gustavohbf/robotoy/design/explosion/explosion0031.png

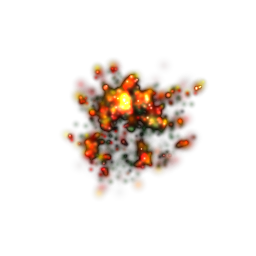
design/explosion/explosion0031.png
