gustavohbf/robotoy/design/3dprint/turret/turret_sliced.PNG

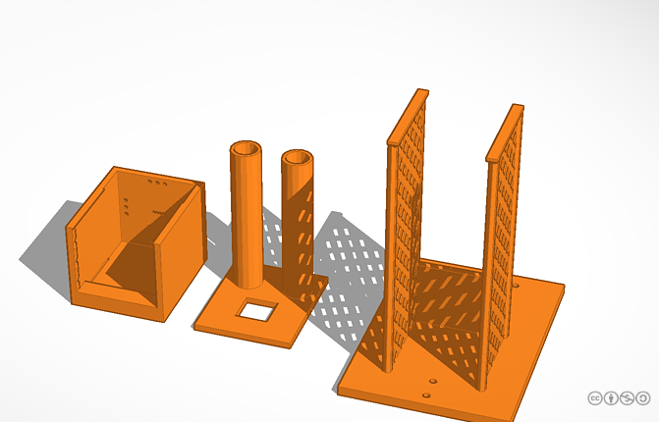
design/3dprint/turret/turret_sliced.PNG
