gustavohbf/robotoy/design/explosion/explosion0000.png

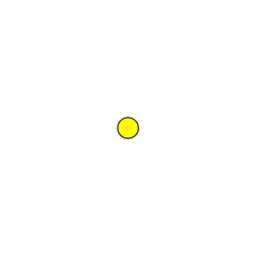
design/explosion/explosion0000.png
