gustavohbf/robotoy/design/explosion/explosion0010.png

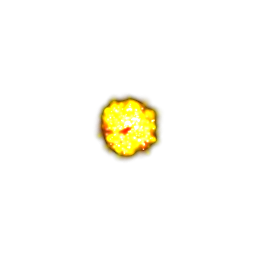
design/explosion/explosion0010.png
