gustavohbf/robotoy/design/explosion/explosion0013.png

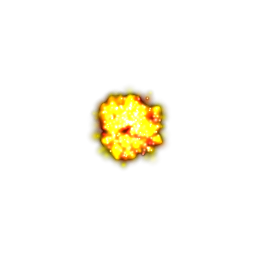
design/explosion/explosion0013.png
