gustavohbf/robotoy/design/explosion/explosion0029.png

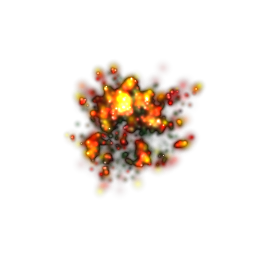
design/explosion/explosion0029.png
