gustavohbf/robotoy/design/explosion/explosion0035.png

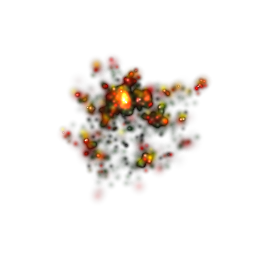
design/explosion/explosion0035.png
