gustavohbf/robotoy/design/explosion/explosion0038.png

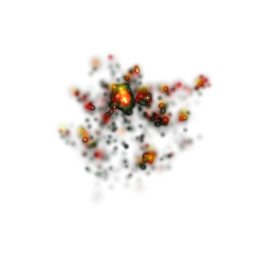
design/explosion/explosion0038.png
