gustavohbf/robotoy/design/explosion/explosion0042.png

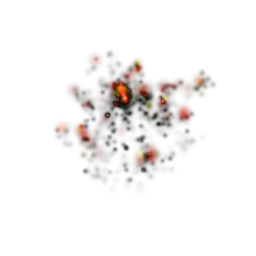
design/explosion/explosion0042.png
