gustavohbf/robotoy/design/explosion/explosion0047.png

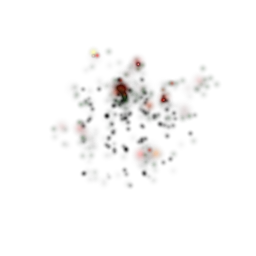
design/explosion/explosion0047.png
