gustavohbf/robotoy/design/explosion/explosion0051.png

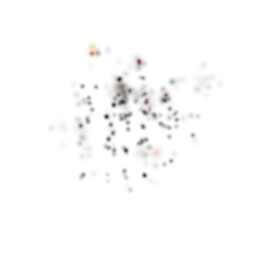
design/explosion/explosion0051.png
