gustavohbf/robotoy/design/explosion/explosion0057.png

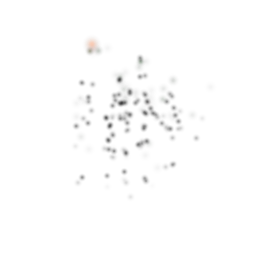
design/explosion/explosion0057.png
