gustavohbf/robotoy/design/explosion/explosion0066.png

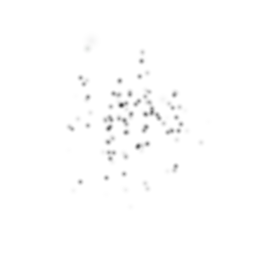
design/explosion/explosion0066.png
