gustavohbf/robotoy/design/explosion/explosion0075.png

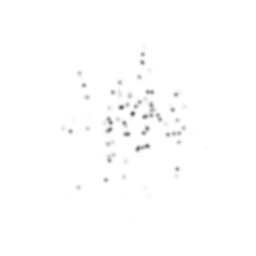
design/explosion/explosion0075.png
