gustavohbf/robotoy/design/explosion/explosion0084.png

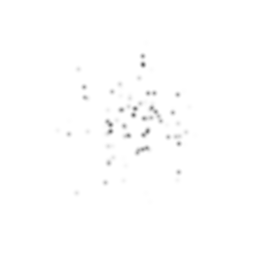
design/explosion/explosion0084.png
