gustavohbf/robotoy/design/explosion/explosion0100.png

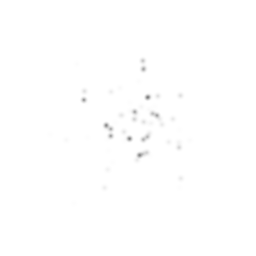
design/explosion/explosion0100.png
