gustavohbf/robotoy/design/explosion/explosion0104.png

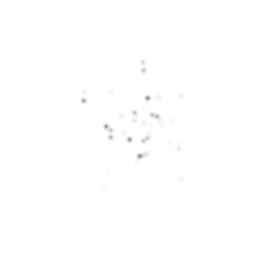
design/explosion/explosion0104.png
