gustavohbf/robotoy/design/explosion/explosion0119.png

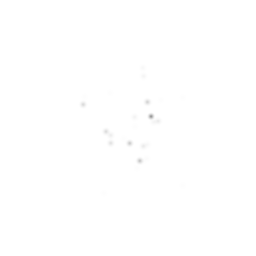
design/explosion/explosion0119.png
