gustavohbf/robotoy/design/sketch/RoboToy_bb.png

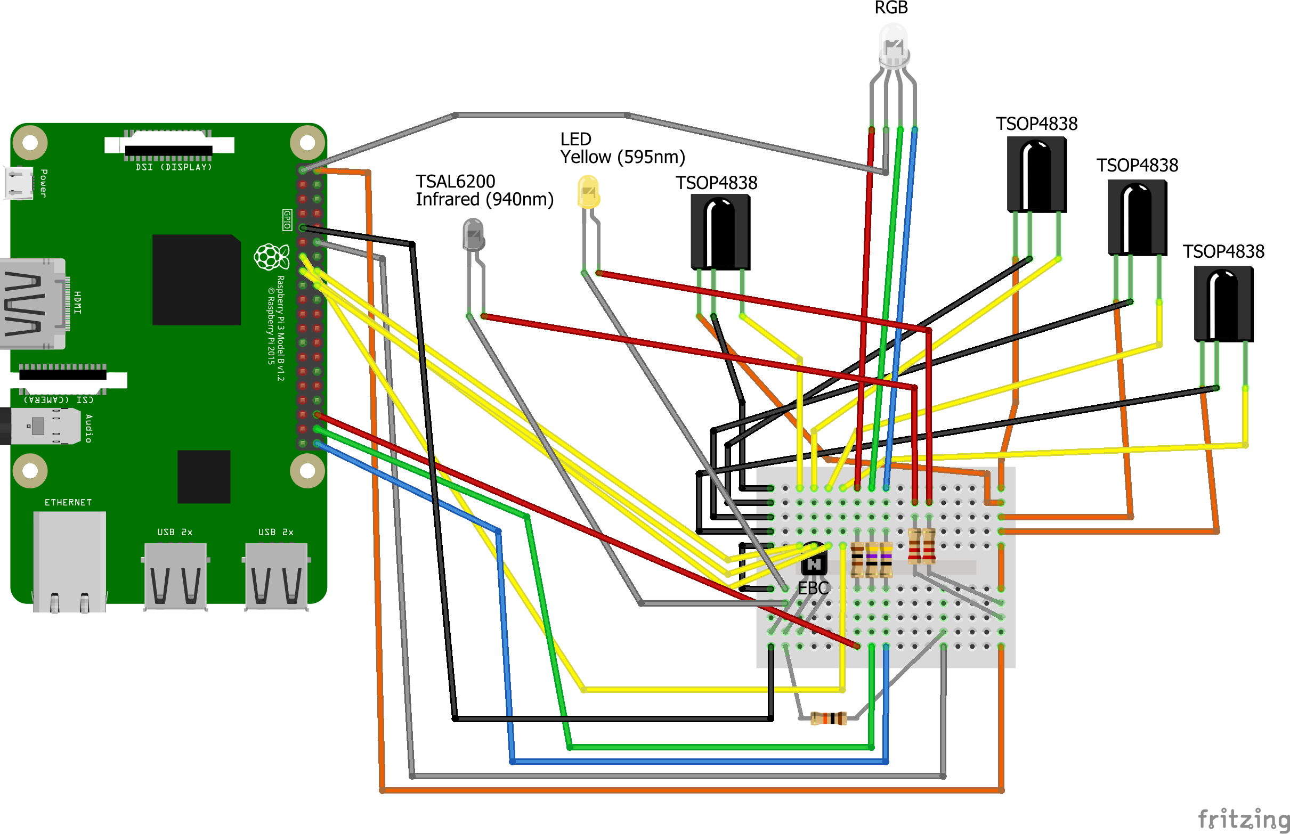
design/sketch/RoboToy_bb.png
