gustavohbf/robotoy/design/sketch/RoboToy_Schematic.png

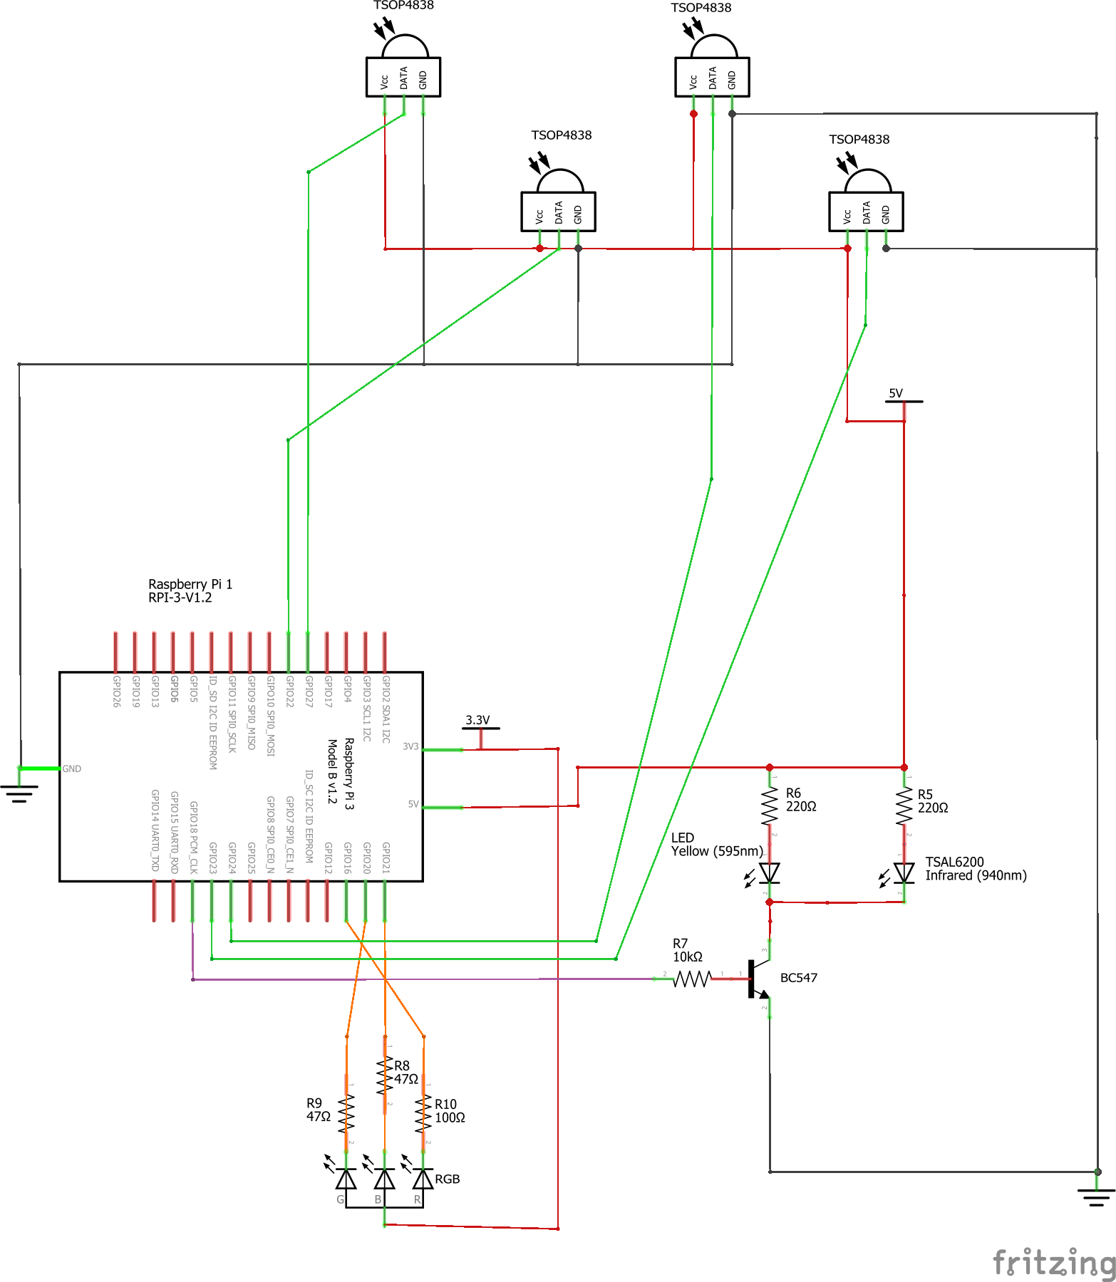
design/sketch/RoboToy_Schematic.png
