gustavohbf/robotoy/src/main/java/org/guga/robotoy/rasp/res/images/background.jpg

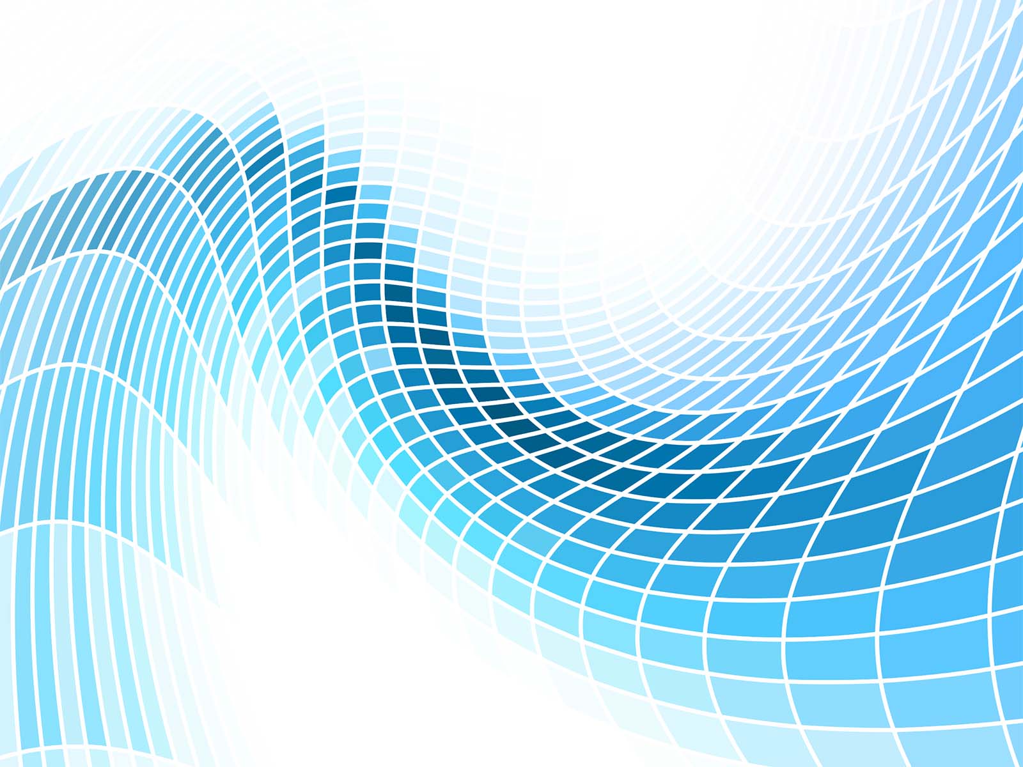
src/main/java/org/guga/robotoy/rasp/res/images/background.jpg
