gustavohbf/robotoy/src/main/java/org/guga/robotoy/rasp/res/images/bigexplosion.png

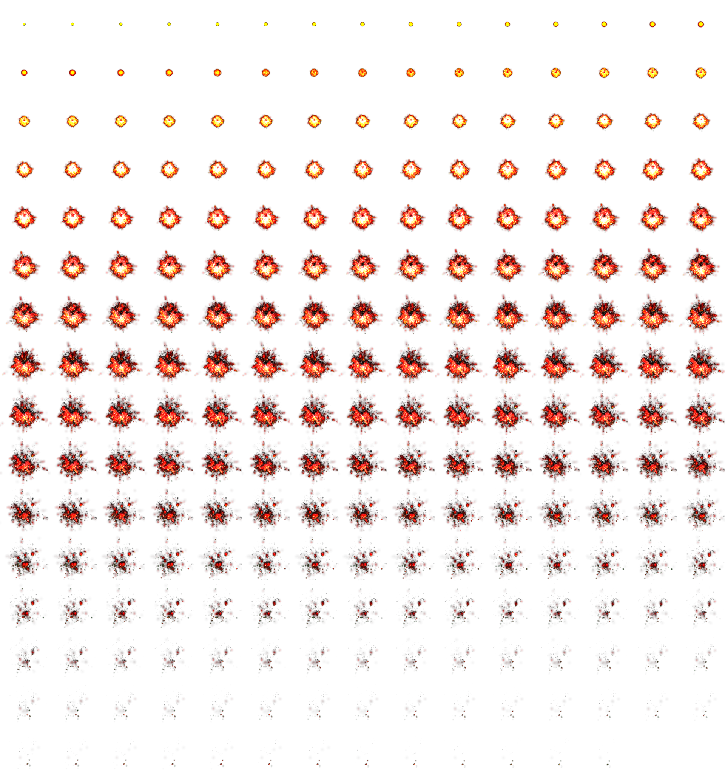
src/main/java/org/guga/robotoy/rasp/res/images/bigexplosion.png
