gustavohbf/robotoy/src/main/java/org/guga/robotoy/rasp/res/images/down.png

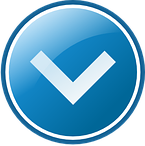
src/main/java/org/guga/robotoy/rasp/res/images/down.png
