gustavohbf/robotoy/src/main/java/org/guga/robotoy/rasp/res/images/engine.png

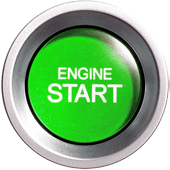
src/main/java/org/guga/robotoy/rasp/res/images/engine.png
