gustavohbf/robotoy/src/main/java/org/guga/robotoy/rasp/res/images/explosion.png

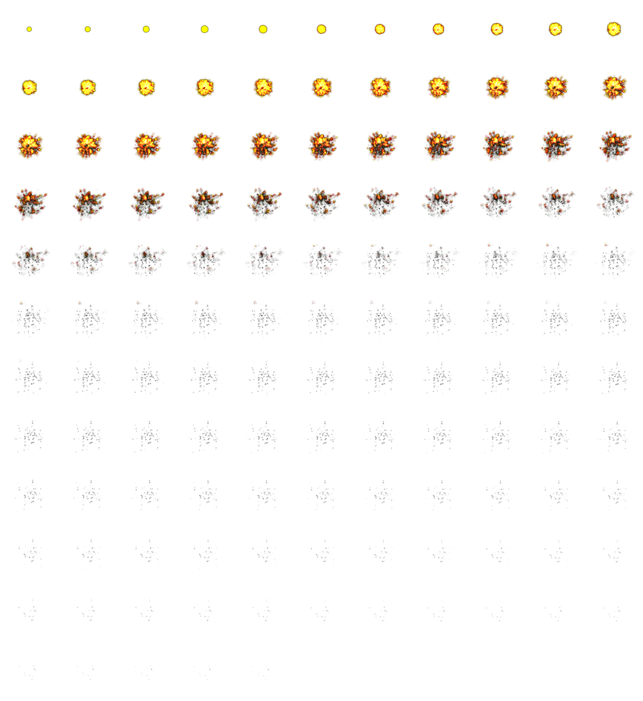
src/main/java/org/guga/robotoy/rasp/res/images/explosion.png
