gustavohbf/robotoy/src/main/java/org/guga/robotoy/rasp/res/images/fire.png

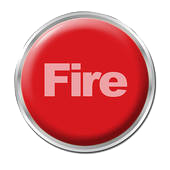
src/main/java/org/guga/robotoy/rasp/res/images/fire.png
