gustavohbf/robotoy/src/main/java/org/guga/robotoy/rasp/res/images/heart.png

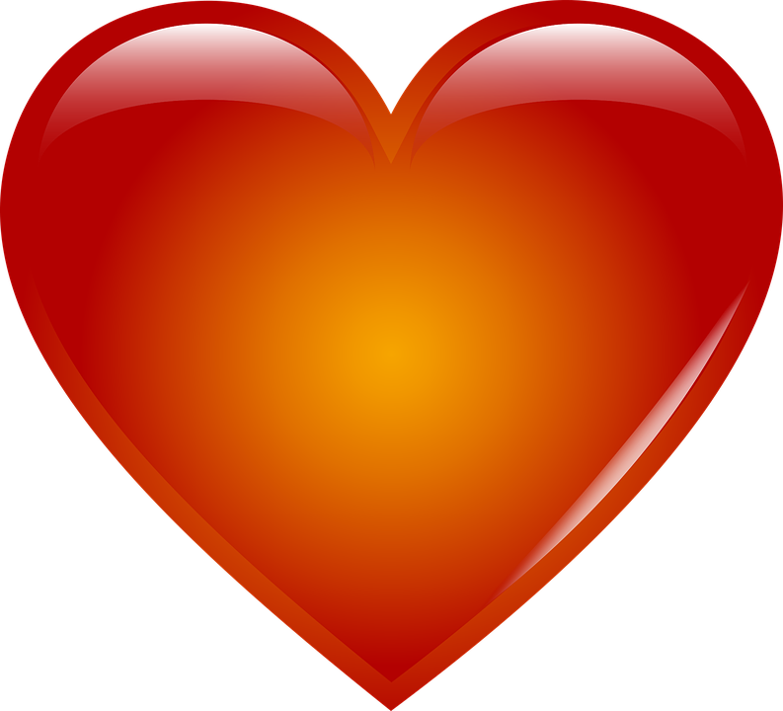
src/main/java/org/guga/robotoy/rasp/res/images/heart.png
