gustavohbf/robotoy/src/main/java/org/guga/robotoy/rasp/res/images/hi_def.png

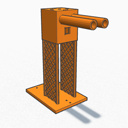
src/main/java/org/guga/robotoy/rasp/res/images/hi_def.png
