gustavohbf/robotoy/src/main/java/org/guga/robotoy/rasp/res/images/left.png

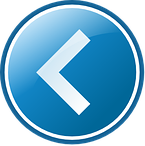
src/main/java/org/guga/robotoy/rasp/res/images/left.png
