gustavohbf/robotoy/src/main/java/org/guga/robotoy/rasp/res/images/right.png

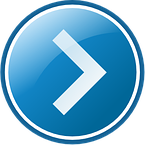
src/main/java/org/guga/robotoy/rasp/res/images/right.png
