gustavohbf/robotoy/src/main/java/org/guga/robotoy/rasp/res/images/up.png

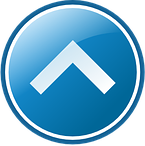
src/main/java/org/guga/robotoy/rasp/res/images/up.png
