gustavohbf/robotoy/src/main/java/org/guga/robotoy/rasp/res/images/wifi0.png

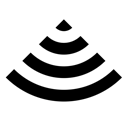
src/main/java/org/guga/robotoy/rasp/res/images/wifi0.png
