gustavohbf/robotoy/design/sketch/RoboToy_solder.png

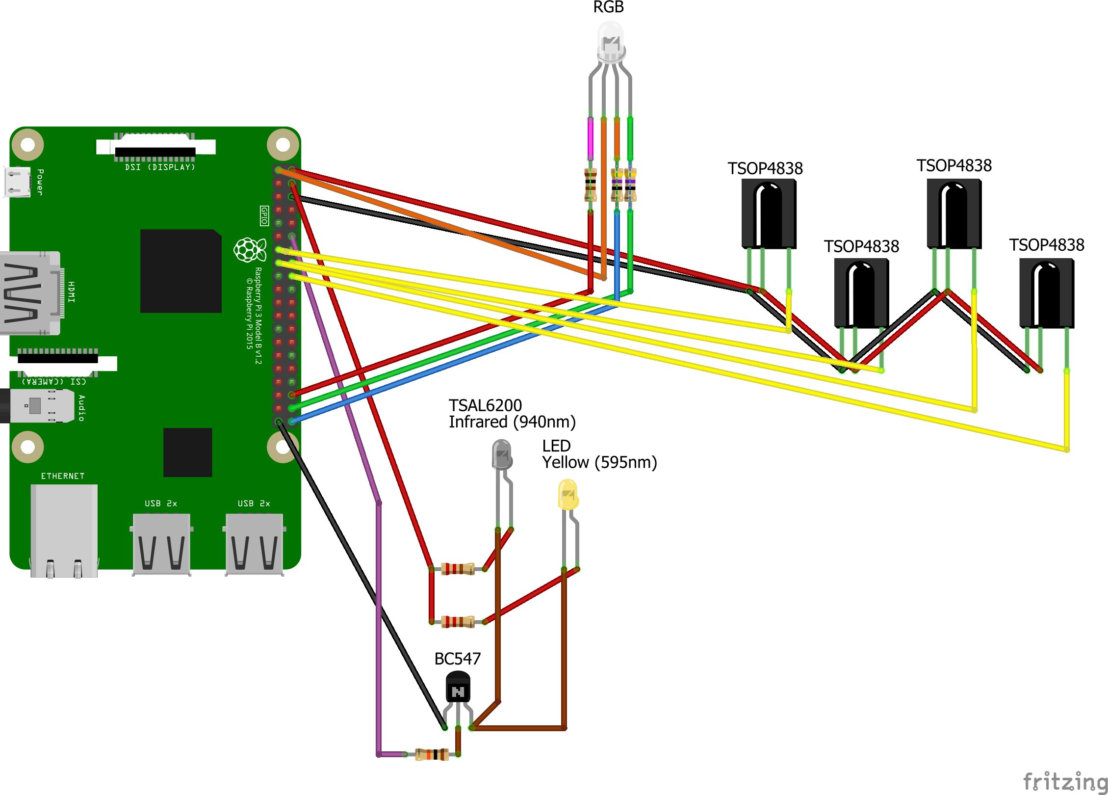
design/sketch/RoboToy_solder.png
